yatara-cc/drink-me/openscad/drink-me.case.scad

include <drink-me.scad>

present() {
     case_3d();
}
