yatara-cc/drink-me/openscad/drink-me.rest.scad

include <drink-me.scad>

present() {
     rest_3d();
}
